haricane8133/graytimer/watchfaceutils/previews/claw.png

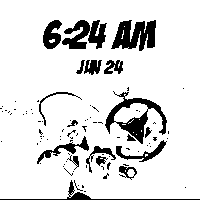
watchfaceutils/previews/claw.png
