haricane8133/graytimer/watchfaceutils/previews/crow.png

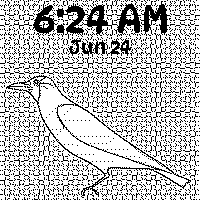
watchfaceutils/previews/crow.png
