haricane8133/graytimer/watchfaceutils/previews/giraffe1.png

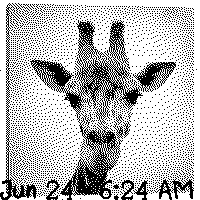
watchfaceutils/previews/giraffe1.png
