haricane8133/graytimer/watchfaceutils/sources/hzd/sawtooth.png

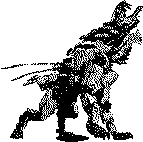
watchfaceutils/sources/hzd/sawtooth.png
