haricane8133/graytimer/watchfaceutils/sources/hzd/stormbird.png

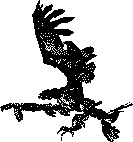
watchfaceutils/sources/hzd/stormbird.png
