haricane8133/graytimer/watchfaceutils/sources/hzd/strider.png

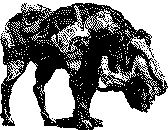
watchfaceutils/sources/hzd/strider.png
