haricane8133/graytimer/watchfaceutils/sources/hzd/watcher.png

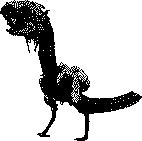
watchfaceutils/sources/hzd/watcher.png
