haricane8133/graytimer/watchfaceutils/sources/sw/mando.png

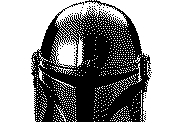
watchfaceutils/sources/sw/mando.png
