haricane8133/graytimer/watchfaceutils/sources/sw/vader.png

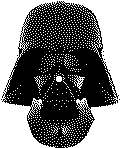
watchfaceutils/sources/sw/vader.png
